UCSD-ECEMAE-148/148-148-spring-2025-final-project-team-10/aruco_marker/latest.jpg

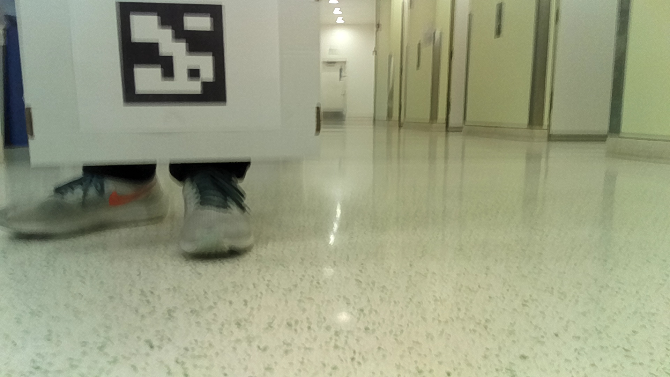
aruco_marker/latest.jpg
