UCSD-ECEMAE-148/148-148-spring-2025-final-project-team-10/media/images/3D-Printed/gpsm2.png

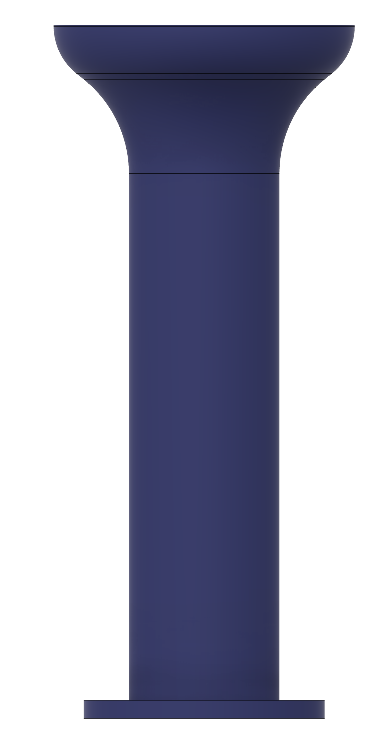
media/images/3D-Printed/gpsm2.png
